miamijerry/daksh-toolchanger-v2/Usermods/MiamiJerry/Modular Lock Bodies/V3_Modular_Original_lock-body-bottom.stl

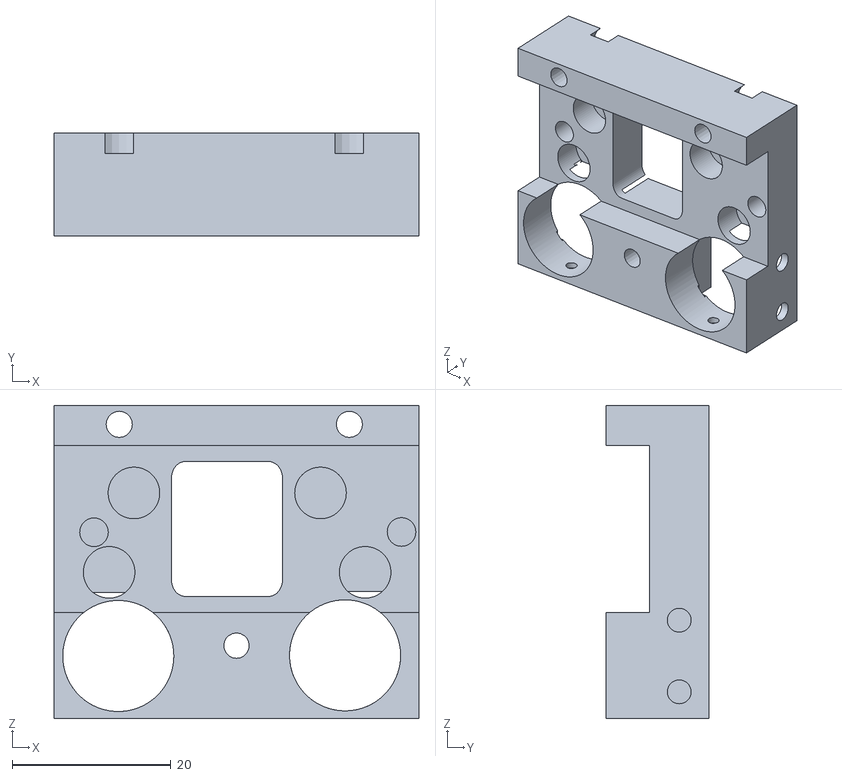
[picture p15: CAD file, 2024-12-02]
Usermods/MiamiJerry/Modular Lock Bodies/V3_Modular_Original_lock-body-bottom.stl
46.0 x 13.0 x 39.5
