miamijerry/daksh-toolchanger-v2/Usermods/MiamiJerry/Dock Bridges/R1_Top_1.stl

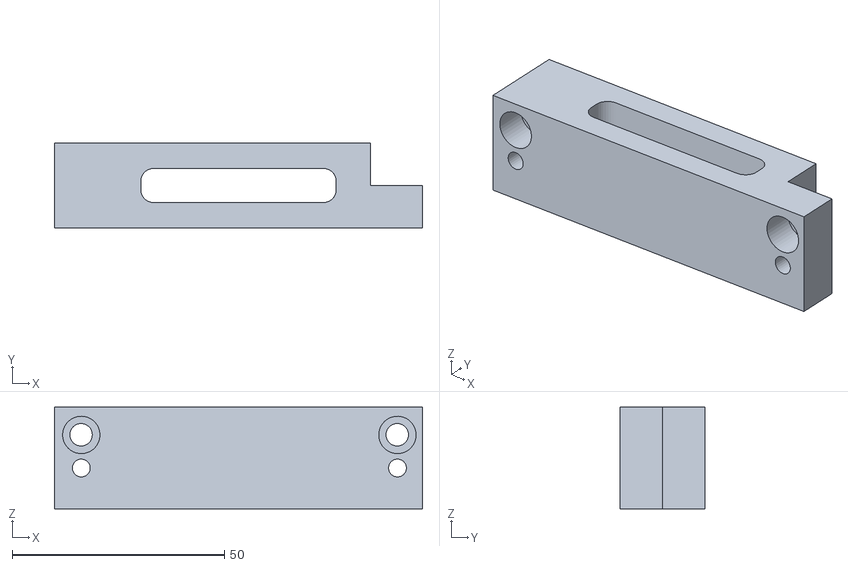
[picture p16: CAD file, 2024-12-02]
Usermods/MiamiJerry/Dock Bridges/R1_Top_1.stl
86.6 x 20.0 x 24.0
