miamijerry/daksh-toolchanger-v2/Usermods/Funday/BTT_Omron_Fan_Body_v1.step

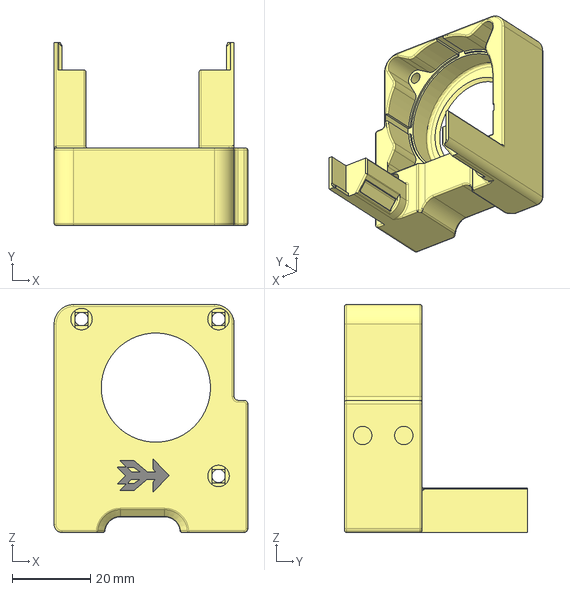
[picture p17: CAD file, 2024-12-01]
Usermods/Funday/BTT_Omron_Fan_Body_v1.step
49.5 x 46.7 x 58.3 mm
