miamijerry/daksh-toolchanger-v2/Usermods/MiamiJerry/Dock Bridges/R1_Top_4.stl

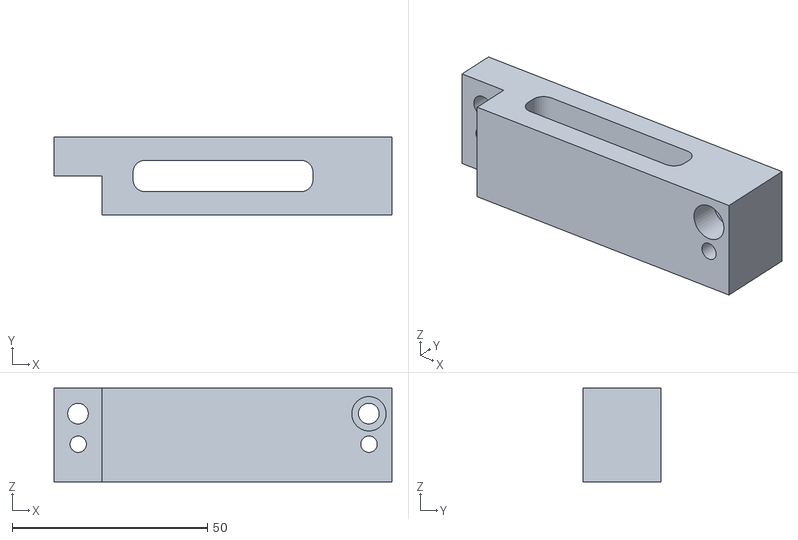
[picture p18: CAD file, 2024-12-02]
Usermods/MiamiJerry/Dock Bridges/R1_Top_4.stl
86.5 x 20.0 x 24.0
