miamijerry/daksh-toolchanger-v2/Usermods/MiamiJerry/Dock Bridges/R1_Bottom_5.stl

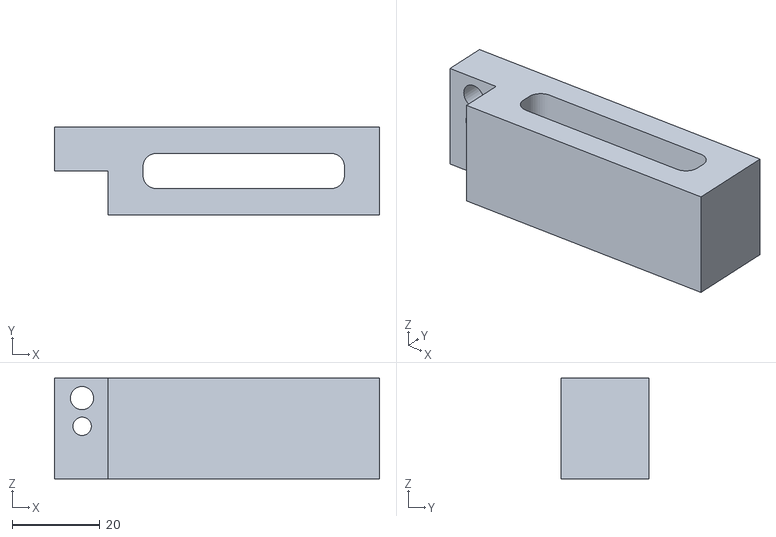
[picture p19: CAD file, 2024-12-02]
Usermods/MiamiJerry/Dock Bridges/R1_Bottom_5.stl
74.2 x 20.0 x 23.0
