miamijerry/daksh-toolchanger-v2/Usermods/MiamiJerry/Dock Bridges/R1_Bottom_4.stl

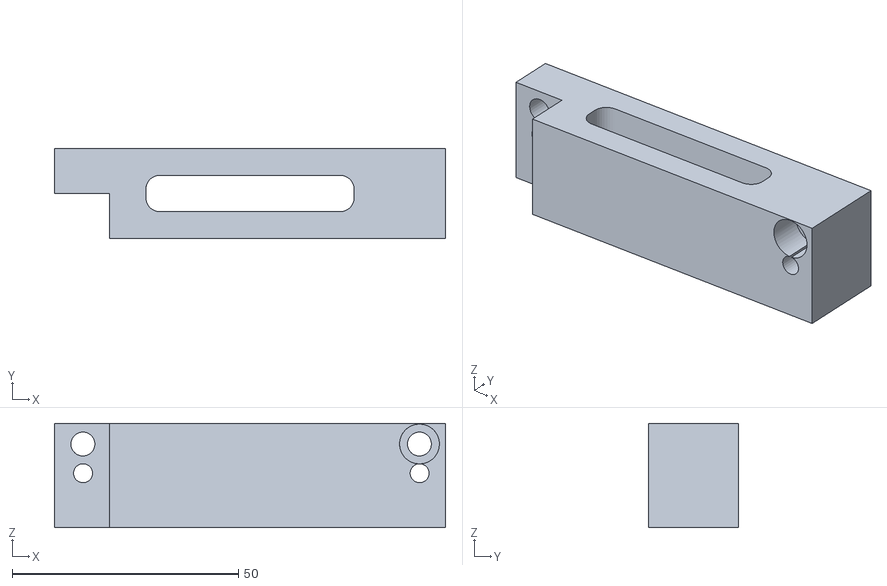
[picture p20: CAD file, 2024-12-02]
Usermods/MiamiJerry/Dock Bridges/R1_Bottom_4.stl
86.4 x 20.0 x 23.0
