miamijerry/daksh-toolchanger-v2/Usermods/Funday/Ebb36_Mount_Sherpa_Mini.step

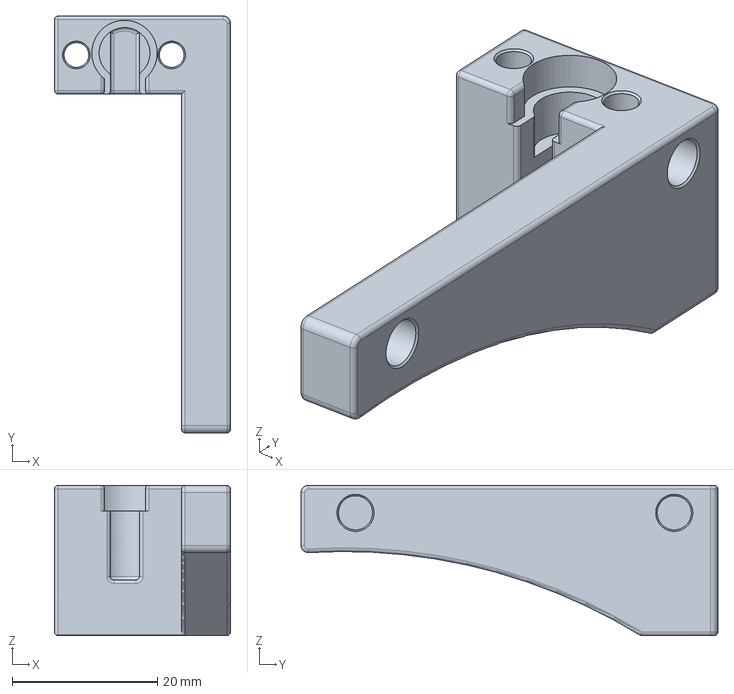
[picture p21: CAD file, 2024-12-01]
Usermods/Funday/Ebb36_Mount_Sherpa_Mini.step
24.2 x 57.4 x 20.7 mm
