miamijerry/daksh-toolchanger-v2/Usermods/Funday/fangrille.step

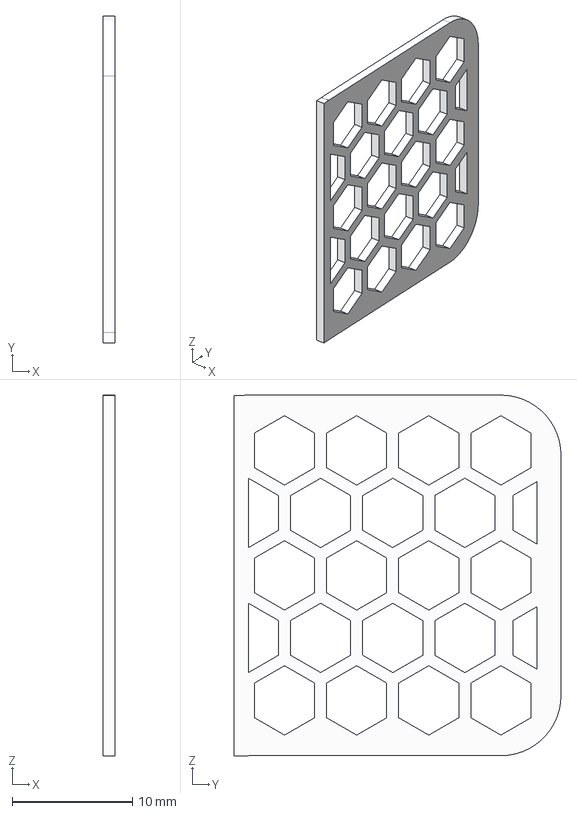
[picture p22: CAD file, 2024-12-01]
Usermods/Funday/fangrille.step
1.00 x 27.2 x 30.0 mm
