miamijerry/daksh-toolchanger-v2/Usermods/Funday/toolbody.step

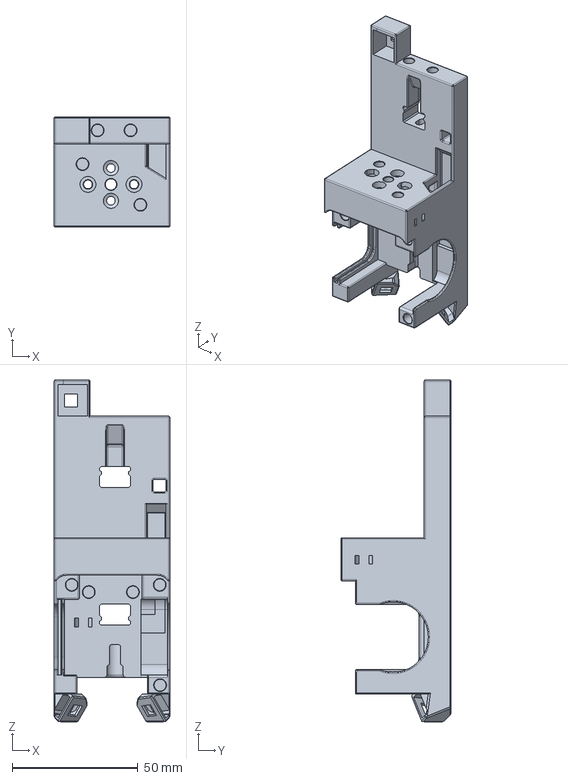
[picture p23: CAD file, 2024-12-01]
Usermods/Funday/toolbody.step
46.0 x 43.8 x 136.0 mm
