miamijerry/daksh-toolchanger-v2/Usermods/Funday/Ebb_36_Cover.step

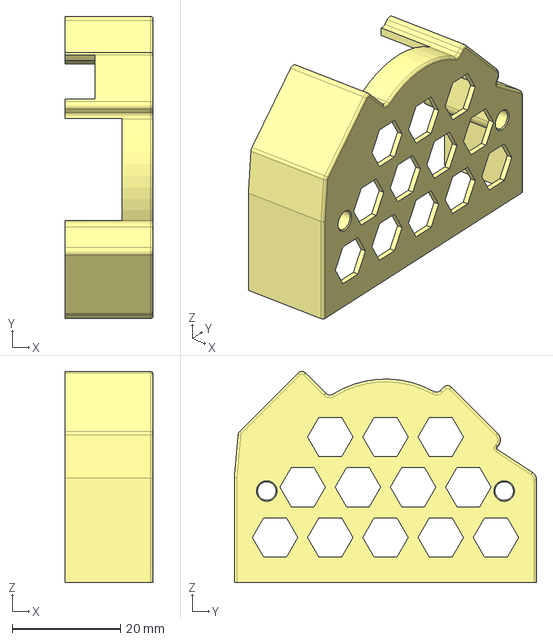
[picture p24: CAD file, 2024-12-01]
Usermods/Funday/Ebb_36_Cover.step
16.3 x 55.9 x 39.0 mm
