miamijerry/daksh-toolchanger-v2/Usermods/Funday/Scaled_101_percent_BTT Fan Body Orion w sensor mount.stl

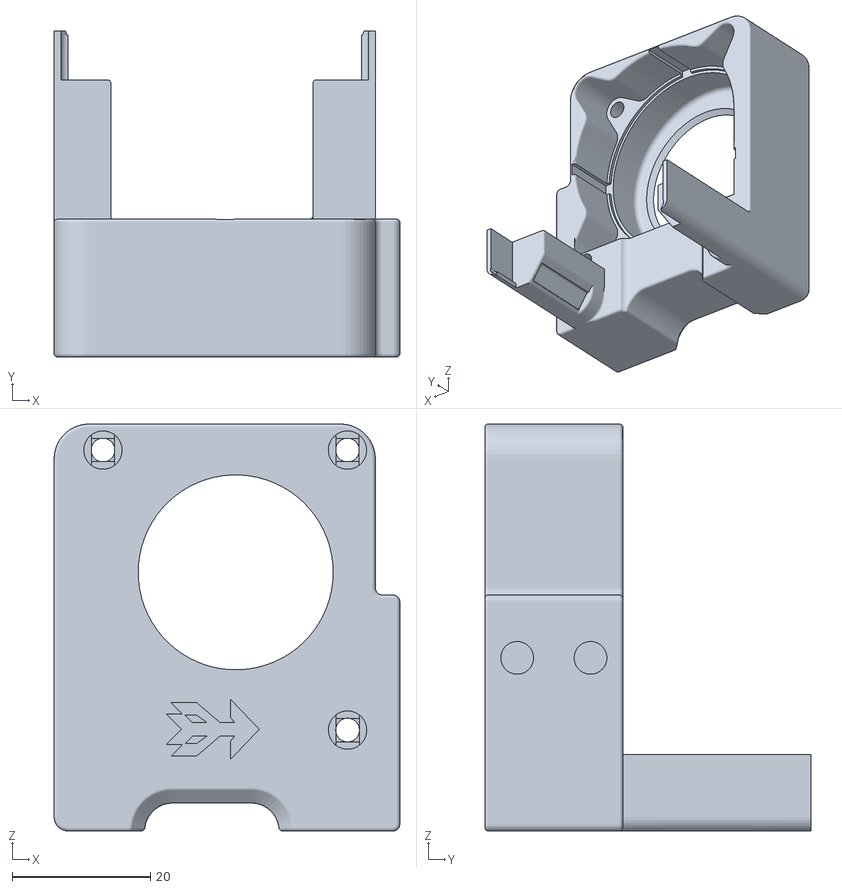
[picture p25: CAD file, 2024-12-01]
Usermods/Funday/Scaled_101_percent_BTT Fan Body Orion w sensor mount.stl
50.0 x 47.2 x 58.8
