miamijerry/daksh-toolchanger-v2/Usermods/Funday/power_umbilical_sleeve.step

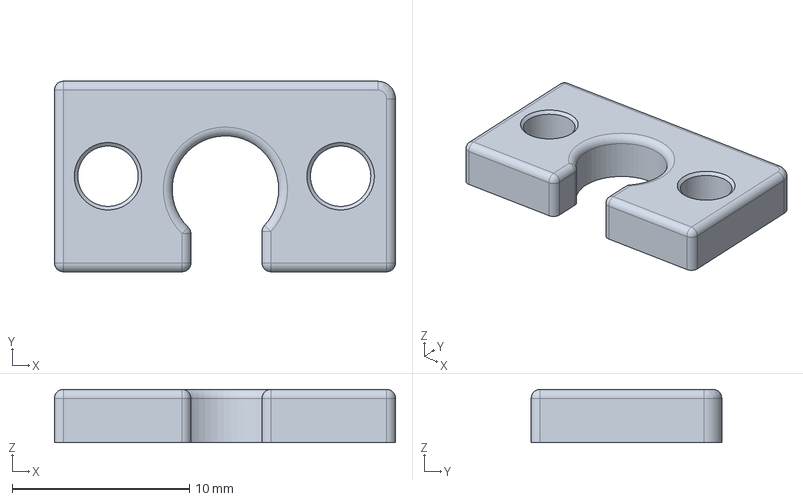
[picture p26: CAD file, 2024-12-01]
Usermods/Funday/power_umbilical_sleeve.step
19.2 x 10.7 x 3.00 mm
